eggsworks/solanum/renders/image-1.png

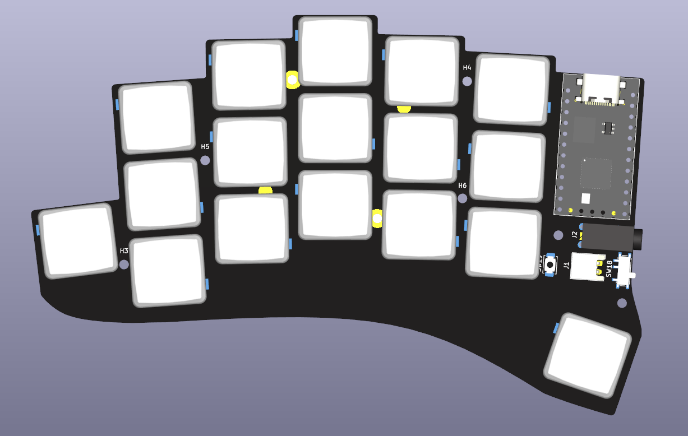
renders/image-1.png
